gianluca-rainis/UHBadge/firmware/tools/buttons.h

#include "firmware.h"

#ifndef UHBADGE_BUTTONS
    #define UHBADGE_BUTTONS

    bool buttonUpPressed();
    bool buttonDownPressed();
    bool buttonLeftPressed();
    bool buttonRightPressed();
#endif
